Newblander/potwatch/img/clip-mount-angle.jpg

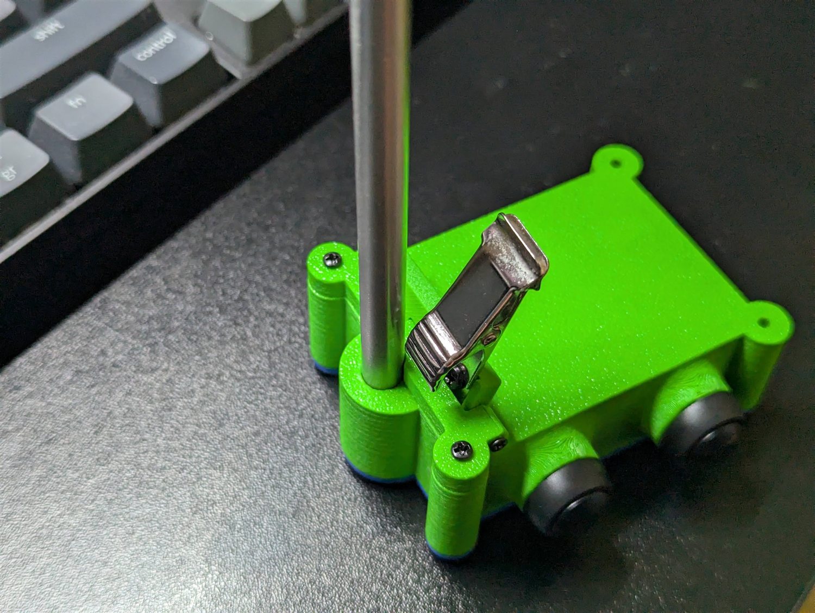
img/clip-mount-angle.jpg
