Newblander/potwatch/img/clip-mount.jpg

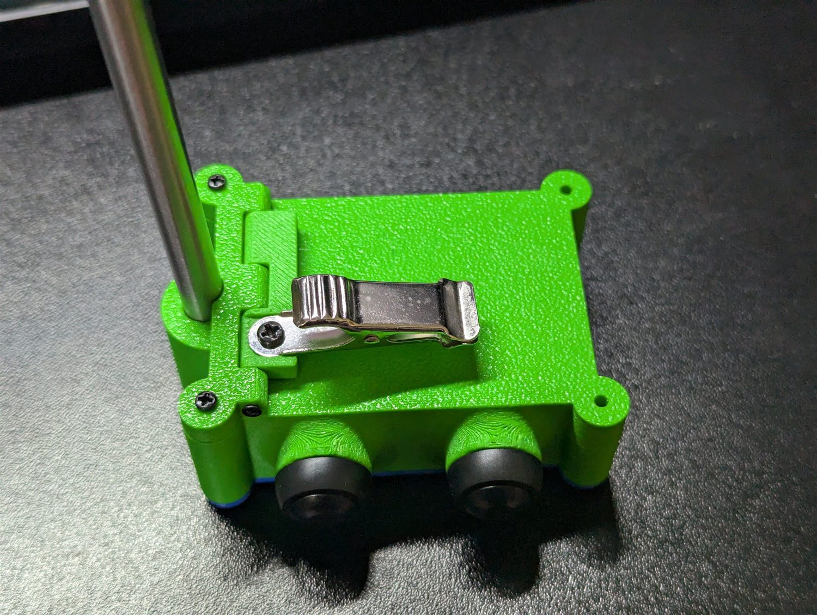
img/clip-mount.jpg
