Newblander/potwatch/img/menu-angle.jpg

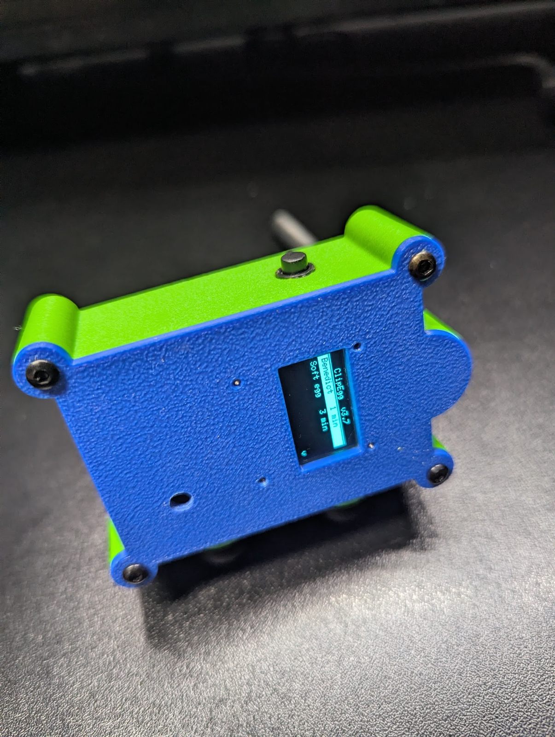
img/menu-angle.jpg
