Newblander/potwatch/img/probe-side.jpg

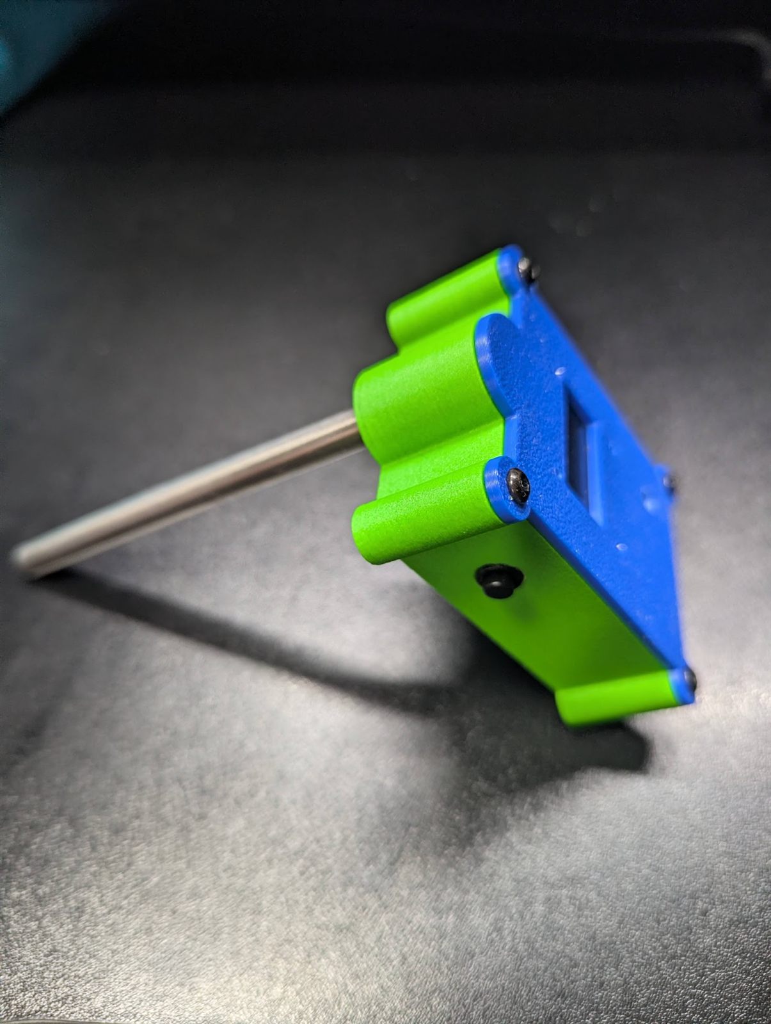
img/probe-side.jpg
