Newblander/potwatch/img/use-on-hob.jpg

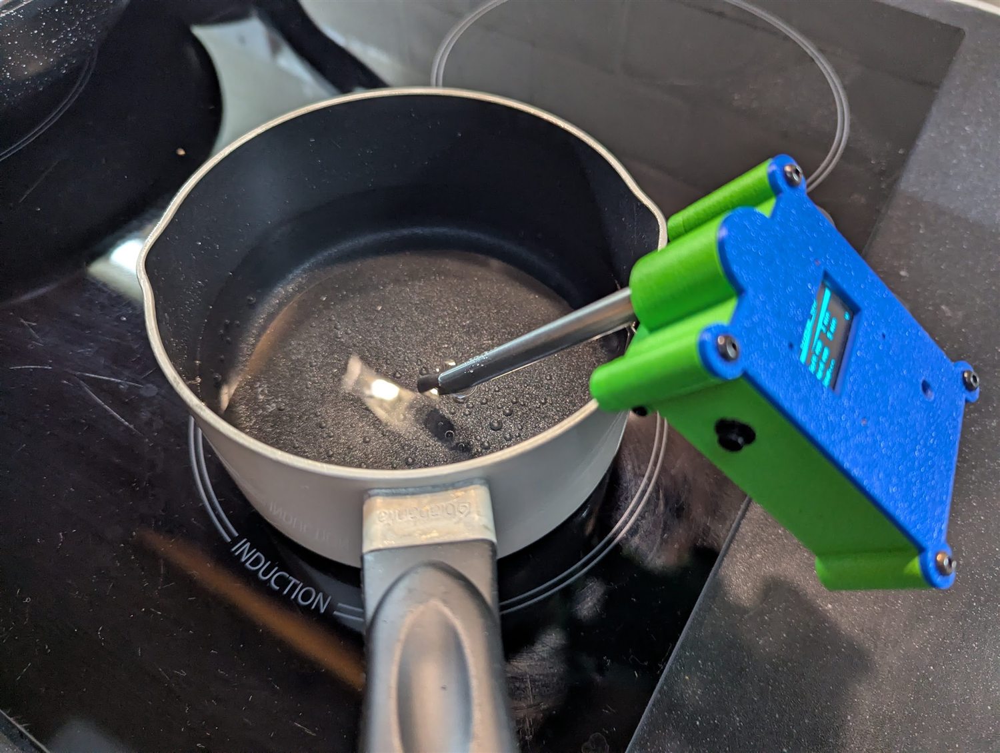
img/use-on-hob.jpg
