Newblander/potwatch/hardware/wiring-diagram.png

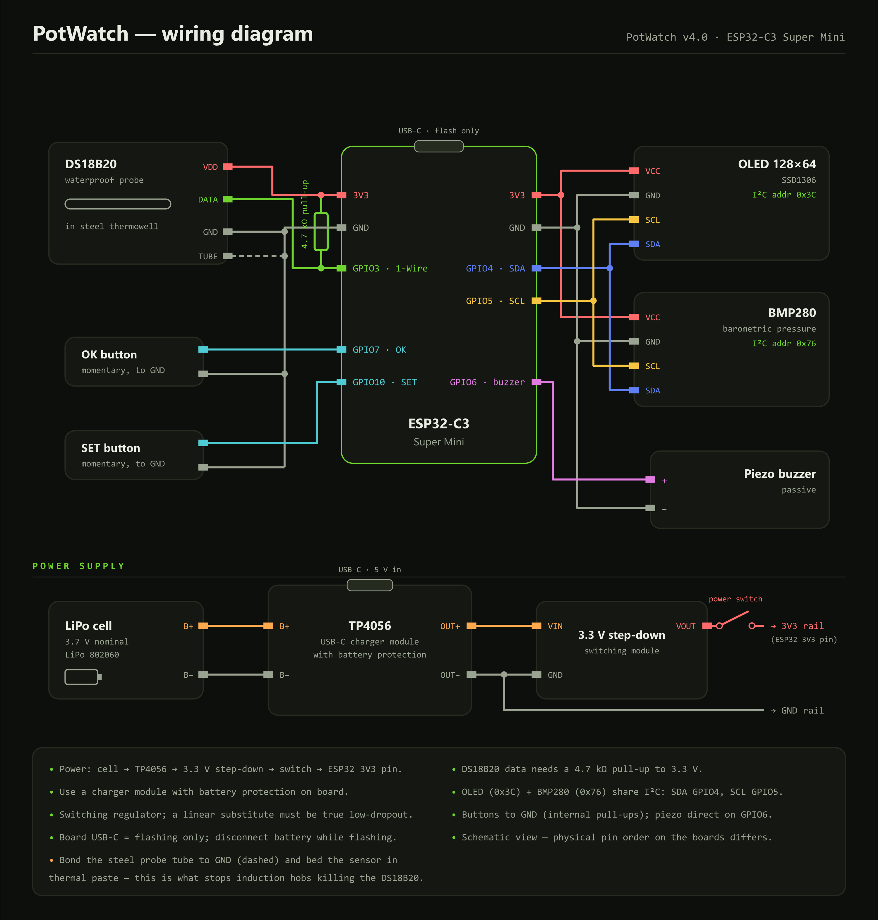
hardware/wiring-diagram.png
